Jan3385/Handheld-electroshock-weapon/PCB/HEC-design.kicad_sch

## KiCad design PCB/HEC-design.kicad_sch (2025-10-21)

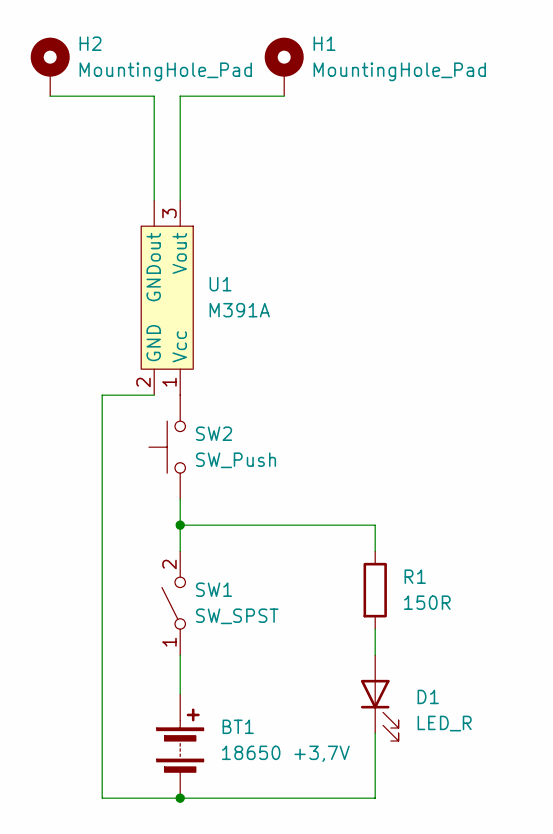
[picture p8: schematic HEC-design.kicad_sch]

Parts:
BT1: 18650 +3,7V
D1: LED_R
H1, H2: MountingHole_Pad
R1: 150R
SW1: SW_SPST
SW2: SW_Push
U1: M391A

Connections:
unnamed: BT1.1 (+), SW1.1 (A)
unnamed: BT1.2 (-), D1.1 (K), U1.2 (GND)
unnamed: D1.2 (A), R1.2
unnamed: H1.1, U1.3 (Vout)
unnamed: H2.1, U1. (GNDout)
unnamed: R1.1, SW1.2 (B), SW2.1
unnamed: SW2.2, U1.1 (Vcc)
